ExploratoryEngineering/pax-counter/src/ble_scan.cpp

#include <Arduino.h>
#include <BLEDevice.h>
#include <BLEUtils.h>
#include <BLEScan.h>
#include <BLEAdvertisedDevice.h>

#include "ble_scan.h"
#include "mac_pool.h"

extern MACAddressPool pool;
BLEScan* pBLEScan;
int scanTime = 5; //In seconds

class MyAdvertisedDeviceCallbacks: public BLEAdvertisedDeviceCallbacks 
{
    void onResult(BLEAdvertisedDevice advertisedDevice) 
    {
        pool.Add(MACSighting(BT, advertisedDevice.getAddress().toString().c_str()));
    }
};

void ble_scanner_setup()
{
    BLEDevice::init("");
    pBLEScan = BLEDevice::getScan(); //create new scan
    pBLEScan->setAdvertisedDeviceCallbacks(new MyAdvertisedDeviceCallbacks());
    pBLEScan->setActiveScan(true); //active scan uses more power, but get results faster
    pBLEScan->setInterval(100);
    pBLEScan->setWindow(99);  // less or equal setInterval value
}

void ble_scan()
{
    Serial.println("Scanning bluetooth...");

    BLEScanResults foundDevices = pBLEScan->start(scanTime, false);
    pBLEScan->clearResults();
    delay(2000);
}
